zakku-shiro/25WSB013_D4/3d models and prints/joint test1.stl

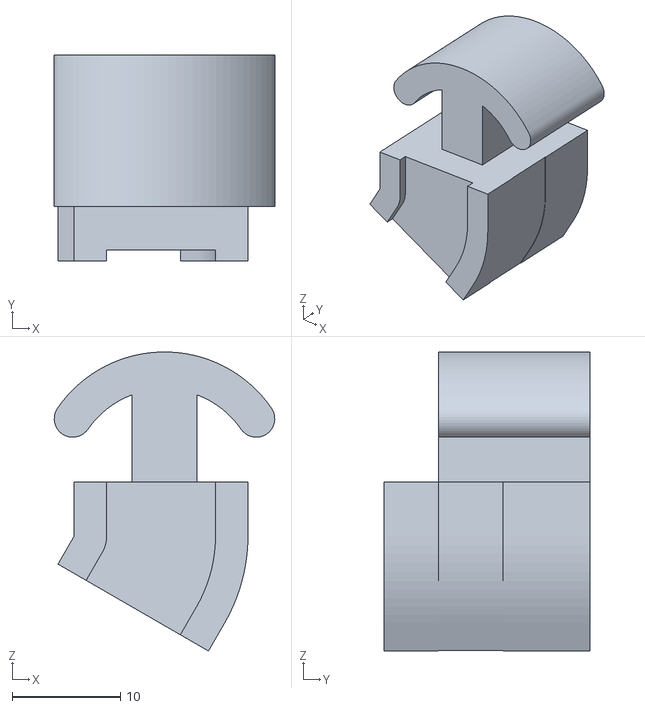
[picture p12: CAD file, 2026-03-17]
3d models and prints/joint test1.stl
20.4 x 19.0 x 27.6
