zakku-shiro/25WSB013_D4/3d models and prints/tractric cone w attachment.stl

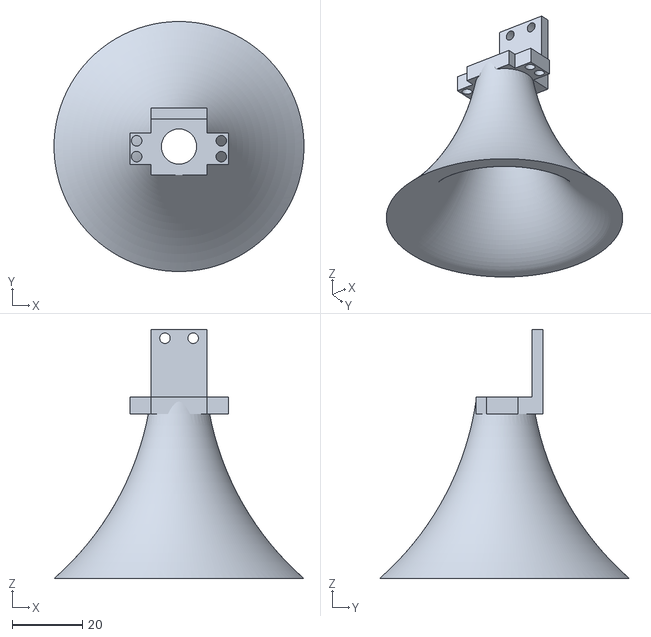
[picture p13: CAD file, 2026-03-17]
3d models and prints/tractric cone w attachment.stl
71.0 x 71.0 x 70.8
