zakku-shiro/25WSB013_D4/3d models and prints/pcb cover plate.stl

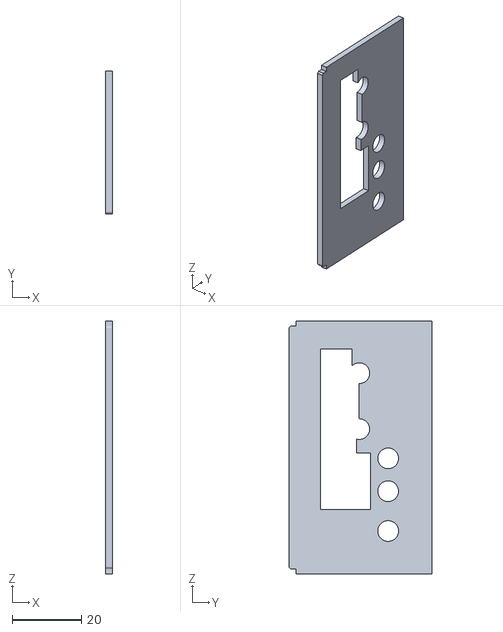
[picture p14: CAD file, 2026-03-17]
3d models and prints/pcb cover plate.stl
2.00 x 41.3 x 73.1
