zakku-shiro/25WSB013_D4/3d models and prints/ultrasonic front.3mf

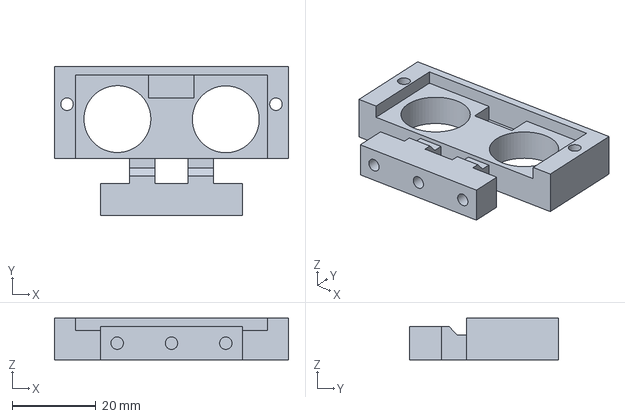
[picture p15: CAD file, 2026-03-17]
3d models and prints/ultrasonic front.3mf
56.0 x 35.6 x 10.0 mm
