zakku-shiro/25WSB013_D4/3d models and prints/joint test2.stl

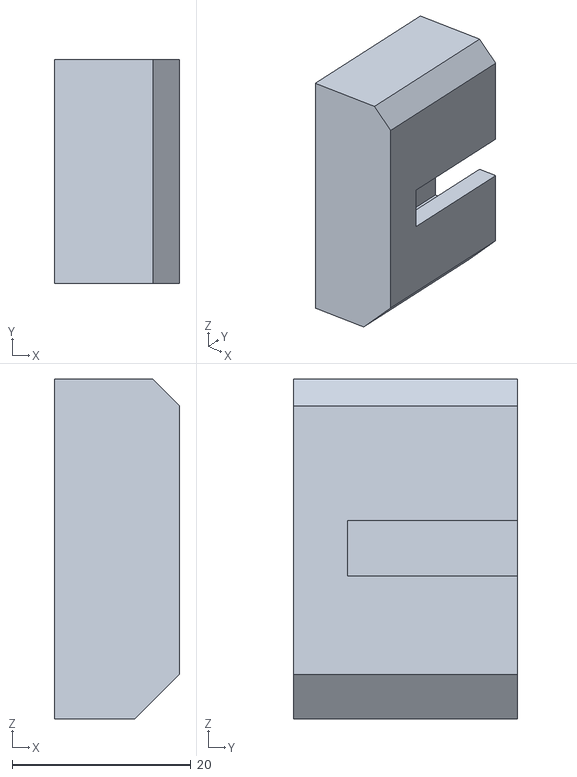
[picture p16: CAD file, 2026-03-17]
3d models and prints/joint test2.stl
14.0 x 25.0 x 38.0
