zakku-shiro/25WSB013_D4/3d models and prints/cam mount.stl

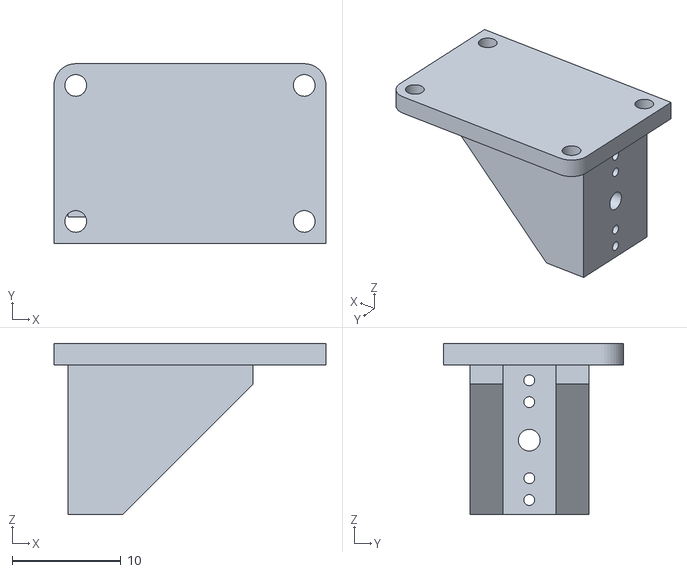
[picture p17: CAD file, 2026-03-17]
3d models and prints/cam mount.stl
25.0 x 16.5 x 15.8
