zakku-shiro/25WSB013_D4/3d models and prints/Tractrix cone1.stl

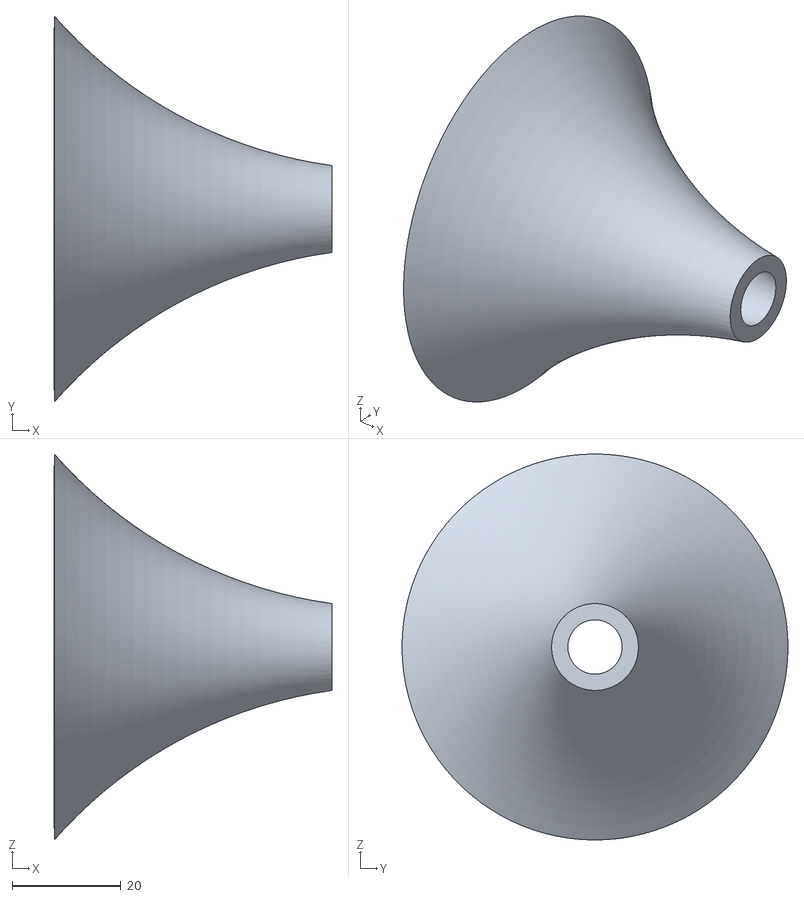
[picture p18: CAD file, 2026-03-17]
3d models and prints/Tractrix cone1.stl
51.1 x 71.0 x 71.0
