zakku-shiro/25WSB013_D4/3d models and prints/mic cone 1.3mf

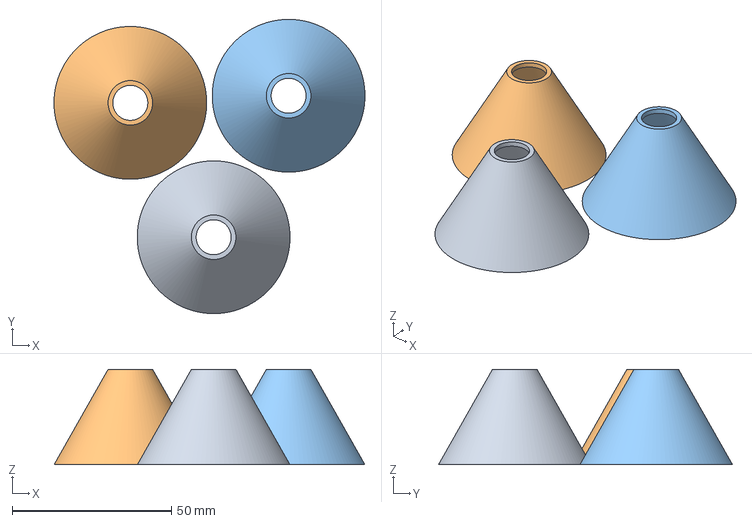
[picture p19: CAD file, 2026-03-17]
3d models and prints/mic cone 1.3mf
97.7 x 92.5 x 30.0 mm
mic cone 1.stl x 3
