zakku-shiro/25WSB013_D4/3d models and prints/ultrasonic back.stl

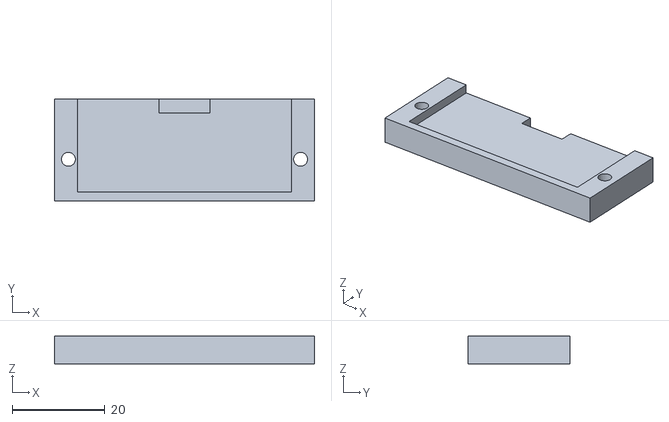
[picture p20: CAD file, 2026-02-05]
3d models and prints/ultrasonic back.stl
56.0 x 22.0 x 6.00
