zakku-shiro/25WSB013_D4/pi/vision/camera.py

import os
import cv2
from config.settings import *

class Camera:
    def __init__(self, is_running_on_pi):
        self.FRAME_WIDTH = None
        self.FRAME_HEIGHT = None
        self.TARGET_FPS = None
        self.camera = None

        self.IS_RUNNING_ON_PI = is_running_on_pi

        if is_running_on_pi:
            self.setup_pi_camera()
        else:
            self.setup_windows_camera()

    def setup_pi_camera(self):
        from picamera2 import Picamera2

        self.FRAME_WIDTH = FRAME_WIDTH
        self.FRAME_HEIGHT = FRAME_HEIGHT
        self.TARGET_FPS = FRAME_RATE

        self.camera = Picamera2()
        config = self.camera.create_preview_configuration(
            main={"size": (self.FRAME_WIDTH, self.FRAME_HEIGHT), "format": "RGB888"},
            controls={
                "FrameRate": self.TARGET_FPS,
                "ExposureValue": PI_ABS_EXPOSURE,
                "AeEnable": False,  # Disable auto-exposure
                "AwbEnable": False, # Disable auto-white-balance
            }
        )
        self.camera.configure(config)
        self.camera.start()

    def setup_windows_camera(self):
        self.camera = cv2.VideoCapture(0)
        if not self.camera.isOpened():
            print("Could not open webcam.")
            exit(1)
        self.FRAME_WIDTH = FRAME_WIDTH
        self.FRAME_HEIGHT = FRAME_HEIGHT
        self.TARGET_FPS = FRAME_RATE
        self.camera.set(cv2.CAP_PROP_FRAME_WIDTH, self.FRAME_WIDTH)
        self.camera.set(cv2.CAP_PROP_FRAME_HEIGHT, self.FRAME_HEIGHT)
        self.camera.set(cv2.CAP_PROP_FPS, self.TARGET_FPS)

        # Prevent auto-exposure
        self.camera.set(cv2.CAP_PROP_AUTO_EXPOSURE, 0.25)
        self.camera.set(cv2.CAP_PROP_AUTO_WB, 0)
        self.camera.set(cv2.CAP_PROP_EXPOSURE, WIN_ABS_EXPOSURE)

    def capture_frame(self):
        if self.IS_RUNNING_ON_PI:
            return self.camera.capture_array()
        else:
            has_captured, frame = self.camera.read()
            if not has_captured:
                print("Failed to capture frame.")
                exit(1)
            return frame

    def release(self):
        if self.IS_RUNNING_ON_PI:
            self.camera.stop()
        else:
            self.camera.release()
